helena-project/squall/software/apps/sniffer/main.c

#include <stdint.h>
#include <stdio.h>
#include <string.h>
#include "nordic_common.h"
#include "nrf_sdm.h"
#include "ble.h"
#include "ble_db_discovery.h"
#include "softdevice_handler.h"
#include "app_util.h"
#include "app_error.h"
#include "ble_advdata_parser.h"
#include "boards.h"
#include "nrf_gpio.h"
#include "pstorage.h"
#include "device_manager.h"
#include "app_trace.h"
#include "ble_hrs_c.h"
#include "ble_bas_c.h"
#include "app_util.h"
#include "led.h"



#define LED_GOT_ADV_PACKET               LED_0                                          /**< Is on when application has asserted. */

#define APPL_LOG                         app_trace_log                                  /**< Debug logger macro that will be used in this file to do logging of debug information over UART. */

#define SEC_PARAM_BOND             1                                  /**< Perform bonding. */
#define SEC_PARAM_MITM             1                                  /**< Man In The Middle protection not required. */
#define SEC_PARAM_IO_CAPABILITIES  BLE_GAP_IO_CAPS_NONE               /**< No I/O capabilities. */
#define SEC_PARAM_OOB              0                                  /**< Out Of Band data not available. */
#define SEC_PARAM_MIN_KEY_SIZE     7                                  /**< Minimum encryption key size. */
#define SEC_PARAM_MAX_KEY_SIZE     16                                 /**< Maximum encryption key size. */

#define SCAN_INTERVAL              0x00A0                             /**< Determines scan interval in units of 0.625 millisecond. */
#define SCAN_WINDOW                0x0050                             /**< Determines scan window in units of 0.625 millisecond. */

#define MIN_CONNECTION_INTERVAL    MSEC_TO_UNITS(7.5, UNIT_1_25_MS)   /**< Determines maximum connection interval in millisecond. */
#define MAX_CONNECTION_INTERVAL    MSEC_TO_UNITS(30, UNIT_1_25_MS)    /**< Determines maximum connection interval in millisecond. */
#define SLAVE_LATENCY              0                                  /**< Determines slave latency in counts of connection events. */
#define SUPERVISION_TIMEOUT        MSEC_TO_UNITS(4000, UNIT_10_MS)    /**< Determines supervision time-out in units of 10 millisecond. */

#define TARGET_UUID                0x180D                             /**< Target device name that application is looking for. */
#define MAX_PEER_COUNT             DEVICE_MANAGER_MAX_CONNECTIONS     /**< Maximum number of peer's application intends to manage. */
#define UUID16_SIZE                2                                  /**< Size of 16 bit UUID */

/**@breif Macro to unpack 16bit unsigned UUID from octet stream. */
#define UUID16_EXTRACT(DST,SRC)                                                                  \
        do                                                                                       \
        {                                                                                        \
            (*(DST)) = (SRC)[1];                                                                 \
            (*(DST)) <<= 8;                                                                      \
            (*(DST)) |= (SRC)[0];                                                                \
        } while(0)

/**@brief Variable length data encapsulation in terms of length and pointer to data */
typedef struct
{
    uint8_t     * p_data;                                         /**< Pointer to data. */
    uint16_t      data_len;                                       /**< Length of data. */
}data_t;

typedef enum
{
    BLE_NO_SCAN,                                                  /**< No advertising running. */
    BLE_WHITELIST_SCAN,                                           /**< Advertising with whitelist. */
    BLE_FAST_SCAN,                                                /**< Fast advertising running. */
} ble_advertising_mode_t;

static ble_gap_scan_params_t        m_scan_param;                        /**< Scan parameters requested for scanning and connection. */
static dm_application_instance_t    m_dm_app_id;                         /**< Application identifier. */

static bool                         m_memory_access_in_progress = false; /**< Flag to keep track of ongoing operations on persistent memory. */

/**
 * @brief Connection parameters requested for connection.
 */
static const ble_gap_conn_params_t m_connection_param =
{
    (uint16_t)MIN_CONNECTION_INTERVAL,   // Minimum connection
    (uint16_t)MAX_CONNECTION_INTERVAL,   // Maximum connection
    0,                                   // Slave latency
    (uint16_t)SUPERVISION_TIMEOUT        // Supervision time-out
};

static void scan_start(void);

#define APPL_LOG                        app_trace_log             /**< Debug logger macro that will be used in this file to do logging of debug information over UART. */

// WARNING: The following macro MUST be un-defined (by commenting out the definition) if the user
// does not have a nRF6350 Display unit. If this is not done, the application will not work.
//#define APPL_LCD_PRINT_ENABLE                                     /**< In case you do not have a functional display unit, disable this flag and observe trace on UART. */

#ifdef APPL_LCD_PRINT_ENABLE

#define APPL_LCD_CLEAR                  nrf6350_lcd_clear         /**< Macro to clear the LCD display.*/
#define APPL_LCD_WRITE                  nrf6350_lcd_write_string  /**< Macro to write a string to the LCD display.*/

#else // APPL_LCD_PRINT_ENABLE

#define APPL_LCD_WRITE(...)             true                      /**< Macro to clear the LCD display defined to do nothing when @ref APPL_LCD_PRINT_ENABLE is not defined.*/
#define APPL_LCD_CLEAR(...)             true                      /**< Macro to write a string to the LCD display defined to do nothing when @ref APPL_LCD_PRINT_ENABLE is not defined.*/

#endif // APPL_LCD_PRINT_ENABLE


/**@brief Function for error handling, which is called when an error has occurred.
 *
 * @warning This handler is an example only and does not fit a final product. You need to analyze
 *          how your product is supposed to react in case of error.
 *
 * @param[in] error_code  Error code supplied to the handler.
 * @param[in] line_num    Line number where the handler is called.
 * @param[in] p_file_name Pointer to the file name.
 */
void app_error_handler(uint32_t error_code, uint32_t line_num, const uint8_t * p_file_name) {
    // APPL_LOG("[APPL]: ASSERT: %s, %d, error 0x%08x\r\n", p_file_name, line_num, error_code);
    // nrf_gpio_pin_set(ASSERT_LED_PIN_NO);

    // This call can be used for debug purposes during development of an application.
    // @note CAUTION: Activating this code will write the stack to flash on an error.
    //                This function should NOT be used in a final product.
    //                It is intended STRICTLY for development/debugging purposes.
    //                The flash write will happen EVEN if the radio is active, thus interrupting
    //                any communication.
    //                Use with care. Un-comment the line below to use.
    // ble_debug_assert_handler(error_code, line_num, p_file_name);

    // On assert, the system can only recover with a reset.
    NVIC_SystemReset();
}


/**@brief Function for asserts in the SoftDevice.
 *
 * @details This function will be called in case of an assert in the SoftDevice.
 *
 * @warning This handler is an example only and does not fit a final product. You need to analyze
 *          how your product is supposed to react in case of Assert.
 * @warning On assert from the SoftDevice, the system can only recover on reset.
 *
 * @param[in] line_num     Line number of the failing ASSERT call.
 * @param[in] p_file_name  File name of the failing ASSERT call.
 */
void assert_nrf_callback(uint16_t line_num, const uint8_t * p_file_name) {
    app_error_handler(0xDEADBEEF, line_num, p_file_name);
}


/**@brief Callback handling device manager events.
 *
 * @details This function is called to notify the application of device manager events.
 *
 * @param[in]   p_handle      Device Manager Handle. For link related events, this parameter
 *                            identifies the peer.
 * @param[in]   p_event       Pointer to the device manager event.
 * @param[in]   event_status  Status of the event.
 */
static ret_code_t device_manager_event_handler(const dm_handle_t* p_handle,
                                               const dm_event_t* p_event,
                                               const ret_code_t event_result) {
    return NRF_SUCCESS;
}


/**@brief Function for handling the Application's BLE Stack events.
 *
 * @param[in]   p_ble_evt   Bluetooth stack event.
 */
static void on_ble_evt(ble_evt_t * p_ble_evt) {
    switch (p_ble_evt->header.evt_id) {
        case BLE_GAP_EVT_ADV_REPORT: {
            led_toggle(LED_GOT_ADV_PACKET);
            break;
        }
        case BLE_GAP_EVT_TIMEOUT:
            break;
        case BLE_GAP_EVT_CONN_PARAM_UPDATE_REQUEST:
            break;
        default:
            break;
    }
}

/**@brief Function for handling the Application's system events.
 *
 * @param[in]   sys_evt   system event.
 */
static void on_sys_evt(uint32_t sys_evt) {
    switch(sys_evt) {
        case NRF_EVT_FLASH_OPERATION_SUCCESS:
        case NRF_EVT_FLASH_OPERATION_ERROR:
            if (m_memory_access_in_progress) {
                m_memory_access_in_progress = false;
                scan_start();
            }
            break;
        default:
            // No implementation needed.
            break;
    }
}


/**@brief Function for dispatching a BLE stack event to all modules with a BLE stack event handler.
 *
 * @details This function is called from the scheduler in the main loop after a BLE stack event has
 *  been received.
 *
 * @param[in]   p_ble_evt   Bluetooth stack event.
 */
static void ble_evt_dispatch(ble_evt_t * p_ble_evt) {
    on_ble_evt(p_ble_evt);
}


/**@brief Function for dispatching a system event to interested modules.
 *
 * @details This function is called from the System event interrupt handler after a system
 *          event has been received.
 *
 * @param[in]   sys_evt   System stack event.
 */
static void sys_evt_dispatch(uint32_t sys_evt) {
    pstorage_sys_event_handler(sys_evt);
    on_sys_evt(sys_evt);
}


/**@brief Function for initializing the BLE stack.
 *
 * @details Initializes the SoftDevice and the BLE event interrupt.
 */
static void ble_stack_init(void) {
    uint32_t err_code;

    // Initialize the SoftDevice handler module.
    SOFTDEVICE_HANDLER_INIT(NRF_CLOCK_LFCLKSRC_RC_250_PPM_8000MS_CALIBRATION, false);

    // Enable BLE stack.
    ble_enable_params_t ble_enable_params;
    memset(&ble_enable_params, 0, sizeof(ble_enable_params));
    ble_enable_params.gatts_enable_params.service_changed = false;
    ble_enable_params.gap_enable_params.role              = BLE_GAP_ROLE_CENTRAL;

    err_code = sd_ble_enable(&ble_enable_params);
    APP_ERROR_CHECK(err_code);

    // Register with the SoftDevice handler module for BLE events.
    err_code = softdevice_ble_evt_handler_set(ble_evt_dispatch);
    APP_ERROR_CHECK(err_code);

    // Register with the SoftDevice handler module for System events.
    err_code = softdevice_sys_evt_handler_set(sys_evt_dispatch);
    APP_ERROR_CHECK(err_code);
}


/**@brief Function for initializing the Device Manager.
 *
 * @details Device manager is initialized here.
 */
static void device_manager_init(void)
{
    dm_application_param_t param;
    dm_init_param_t        init_param;

    uint32_t              err_code;

    err_code = pstorage_init();
    APP_ERROR_CHECK(err_code);

    // Clear all bonded devices if user requests to.
    init_param.clear_persistent_data = false;
        //((nrf_gpio_pin_read(BOND_DELETE_ALL_BUTTON_ID) == 0)? true: false);

    err_code = dm_init(&init_param);
    APP_ERROR_CHECK(err_code);

    memset(&param.sec_param, 0, sizeof (ble_gap_sec_params_t));

    // Event handler to be registered with the module.
    param.evt_handler            = device_manager_event_handler;

    // Service or protocol context for device manager to load, store and apply on behalf of application.
    // Here set to client as application is a GATT client.
    param.service_type           = DM_PROTOCOL_CNTXT_GATT_CLI_ID;

    // Secuirty parameters to be used for security procedures.
    param.sec_param.bond         = SEC_PARAM_BOND;
    param.sec_param.mitm         = SEC_PARAM_MITM;
    param.sec_param.io_caps      = SEC_PARAM_IO_CAPABILITIES;
    param.sec_param.oob          = SEC_PARAM_OOB;
    param.sec_param.min_key_size = SEC_PARAM_MIN_KEY_SIZE;
    param.sec_param.max_key_size = SEC_PARAM_MAX_KEY_SIZE;
    param.sec_param.kdist_periph.enc = 1;
    param.sec_param.kdist_periph.id  = 1;

    err_code = dm_register(&m_dm_app_id,&param);
    APP_ERROR_CHECK(err_code);
}


/** @brief Function for the Power manager.
 */
static void power_manage(void) {
    uint32_t err_code = sd_app_evt_wait();
    APP_ERROR_CHECK(err_code);
}

/**
 * @brief Database discovery collector initialization.
 */
static void db_discovery_init(void) {
    uint32_t err_code = ble_db_discovery_init();
    APP_ERROR_CHECK(err_code);
}


/**@breif Function to start scanning.
 */
static void scan_start(void) {
    uint32_t            err_code;
    uint32_t            count;

    // Verify if there is any flash access pending, if yes delay starting scanning until
    // it's complete.
    err_code = pstorage_access_status_get(&count);
    APP_ERROR_CHECK(err_code);

    if (count != 0) {
        m_memory_access_in_progress = true;
        return;
    }

    // No devices in whitelist, hence non selective performed.
    m_scan_param.active       = 0;            // Active scanning set.
    m_scan_param.selective    = 0;            // Selective scanning not set.
    m_scan_param.interval     = SCAN_INTERVAL;// Scan interval.
    m_scan_param.window       = SCAN_WINDOW;  // Scan window.
    m_scan_param.p_whitelist  = NULL;         // No whitelist provided.
    m_scan_param.timeout      = 0x0000;       // No timeout.

    err_code = sd_ble_gap_scan_start(&m_scan_param);
    APP_ERROR_CHECK(err_code);
}

int main(void) {
    // Initialization of various modules.
    led_init(LED_GOT_ADV_PACKET);

    ble_stack_init();

    device_manager_init();
    db_discovery_init();

    // Start scanning for peripherals and initiate connection
    // with devices that advertise Heart Rate UUID.
    scan_start();

    while (1) {
        power_manage();
    }
}
