helena-project/squall/software/apps/powerblade/eddystone.h

#ifndef __EDDYSTONE_H
#define __EDDYSTONE_H

// Physical Web
#define PHYSWEB_SERVICE_ID  0xFEAA
#define PHYSWEB_URL_TYPE    0x10    // Denotes URLs (vs URIs or TLM data)
#define PHYSWEB_TX_POWER    0xBA    // Tx Power. Measured at 1 m plus 41 dBm. (who cares)

#define PHYSWEB_URLSCHEME_HTTPWWW   0x00    // http://www.
#define PHYSWEB_URLSCHEME_HTTPSWWW  0x01    // https://www.
#define PHYSWEB_URLSCHEME_HTTP      0x02    // http://
#define PHYSWEB_URLSCHEME_HTTPS     0x03    // https://

#define PHYSWEB_URLEND_COMSLASH 0x00    // .com/
#define PHYSWEB_URLEND_ORGSLASH 0x01    // .org/
#define PHYSWEB_URLEND_EDUSLASH 0x02    // .edu/
#define PHYSWEB_URLEND_COM      0x07    // .com
#define PHYSWEB_URLEND_ORG      0x08    // .org
#define PHYSWEB_URLEND_EDU      0x09    // .edu


#endif
